sparkfun/Variable_Load/Firmware/Variable_Load/Variable_Load.cydsn/cyapicallbacks.h

/* ========================================
 *
 * Copyright YOUR COMPANY, THE YEAR
 * All Rights Reserved
 * UNPUBLISHED, LICENSED SOFTWARE.
 *
 * CONFIDENTIAL AND PROPRIETARY INFORMATION
 * WHICH IS THE PROPERTY OF your company.
 *
 * ========================================
*/
#ifndef CYAPICALLBACKS_H
#define CYAPICALLBACKS_H
    
    /*Define your macro callbacks here */
    /*For more information, refer to the Macro Callbacks topic in the PSoC Creator Help.*/
#define PIDIsr_INTERRUPT_INTERRUPT_CALLBACK
    void PIDIsr_Interrupt_InterruptCallback();
 
#endif /* CYAPICALLBACKS_H */   
/* [] */
